jdenish1/MY_Kyria_Handwired_Split_Keyboard_Build/Info/Kyria_Handwired Key Matrix.jpeg

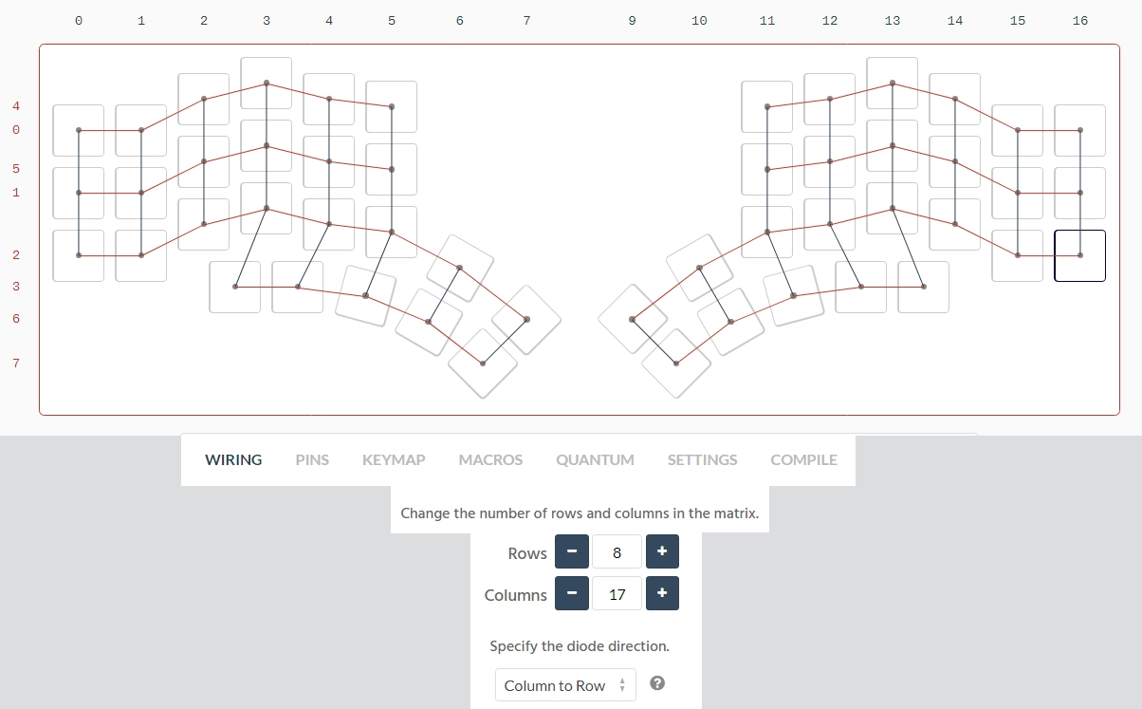
Info/Kyria_Handwired Key Matrix.jpeg
