jdenish1/MY_Kyria_Handwired_Split_Keyboard_Build/Pics/4 - Left Side 1.jpg

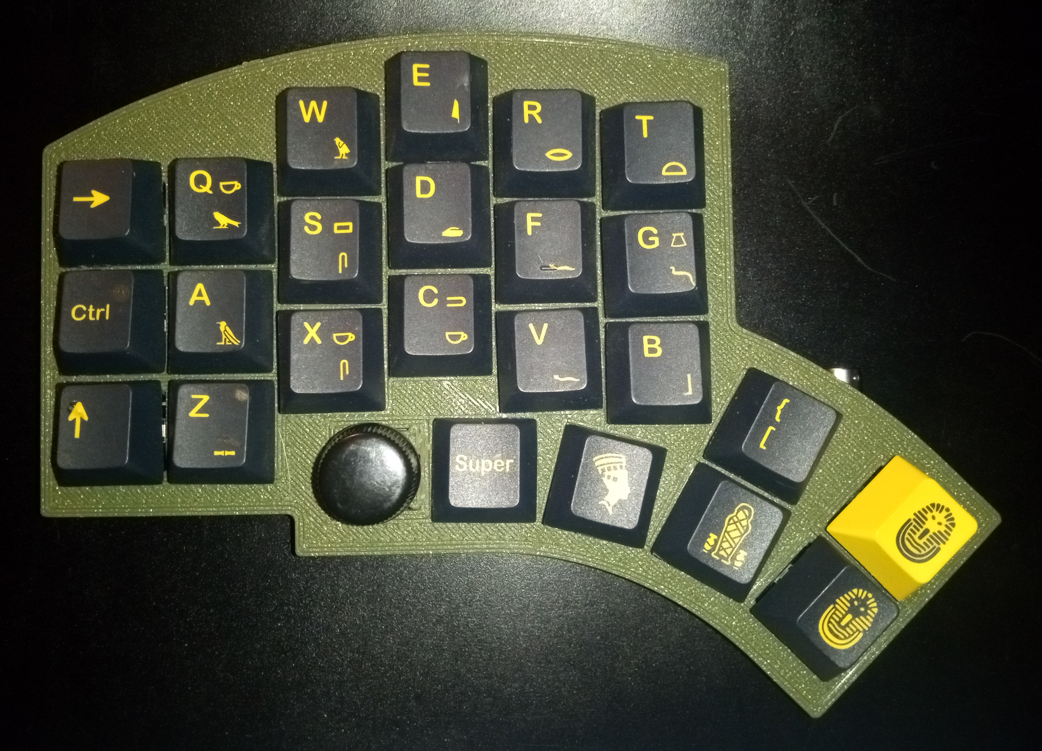
Pics/4 - Left Side 1.jpg
