jdenish1/MY_Kyria_Handwired_Split_Keyboard_Build/Pics/5 - Right Side 1.jpg

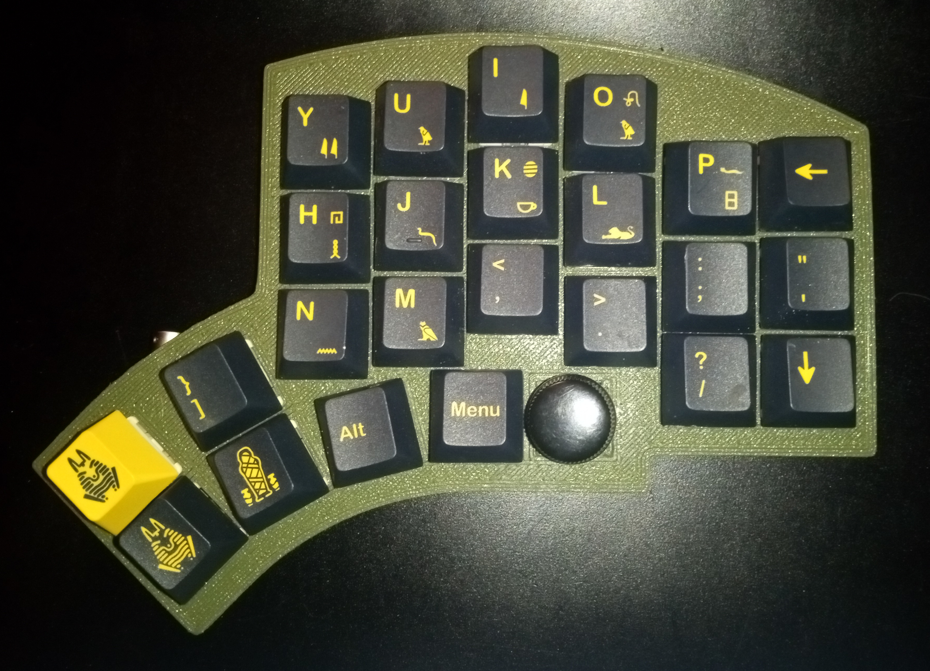
Pics/5 - Right Side 1.jpg
