jdenish1/MY_Kyria_Handwired_Split_Keyboard_Build/Pics/6 - Left Side 2.jpg

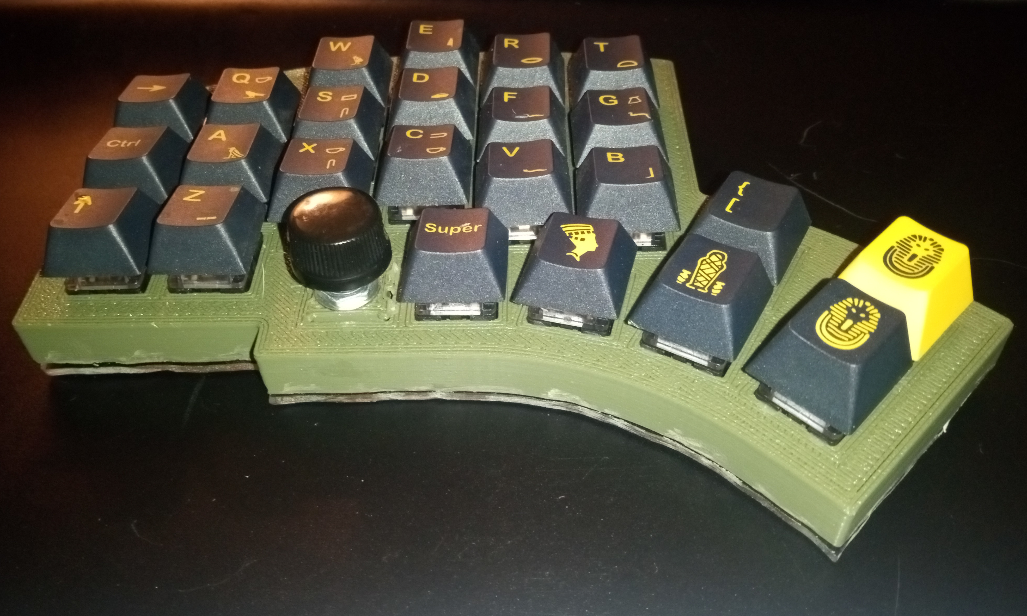
Pics/6 - Left Side 2.jpg
