jdenish1/MY_Kyria_Handwired_Split_Keyboard_Build/Pics/7 - Right Side 2.jpg

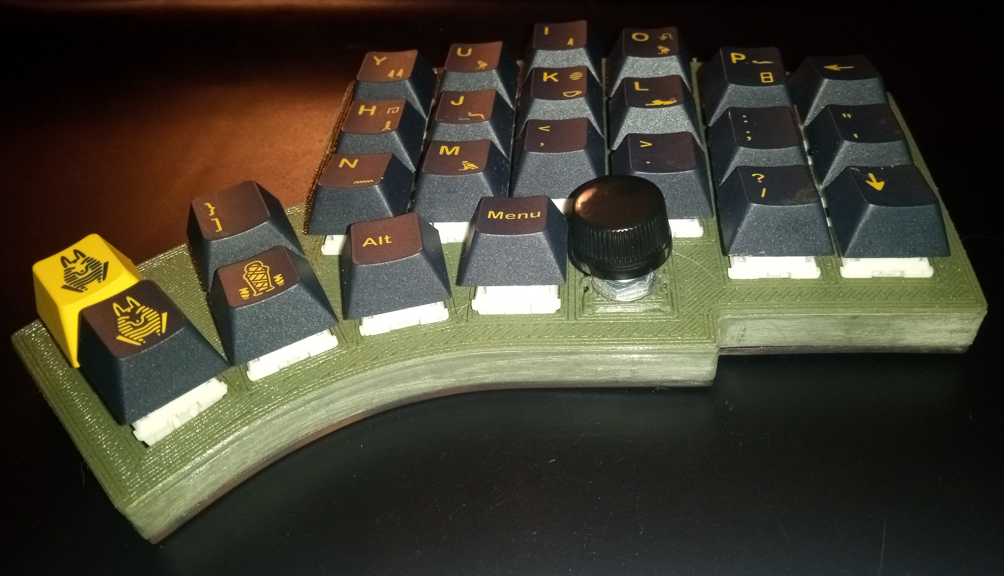
Pics/7 - Right Side 2.jpg
