jdenish1/MY_Kyria_Handwired_Split_Keyboard_Build/Pics/9 - Right Side 3.jpg

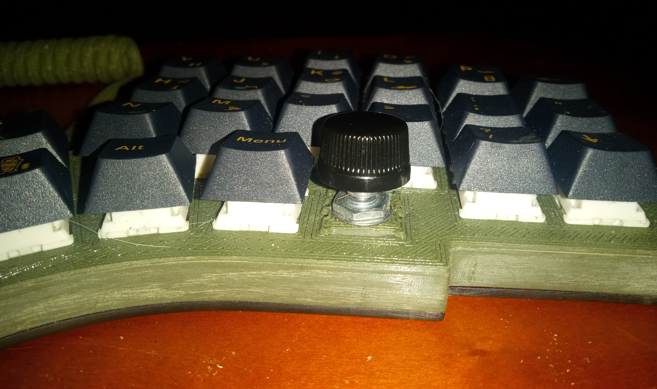
Pics/9 - Right Side 3.jpg
