jdenish1/MY_Kyria_Handwired_Split_Keyboard_Build/Pics/11 - XS6 Cable Closeup 2.jpg

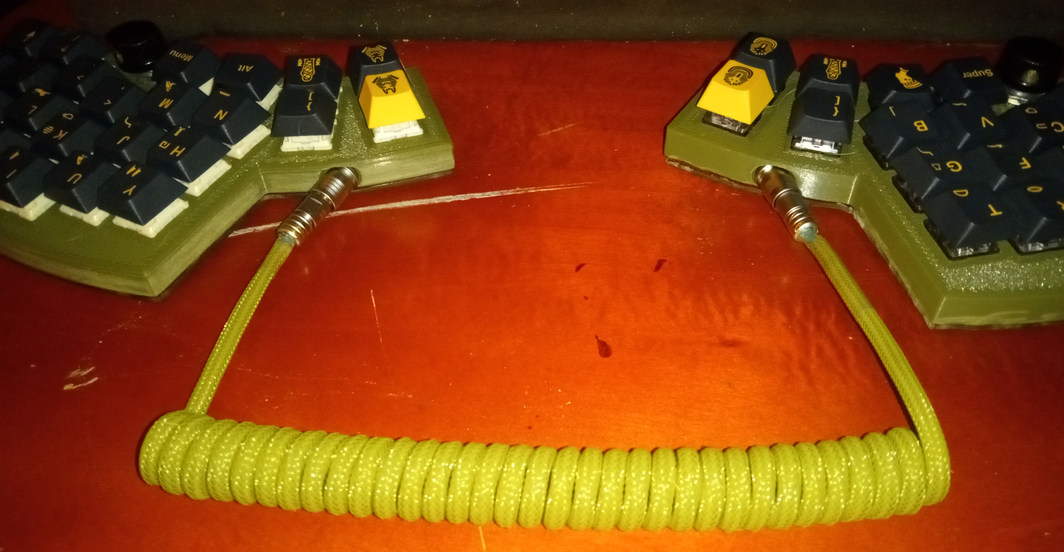
Pics/11 - XS6 Cable Closeup 2.jpg
