jdenish1/MY_Kyria_Handwired_Split_Keyboard_Build/Pics/15 - Left Side Acrylic Back Cover for Kyria_Handwired.jpg

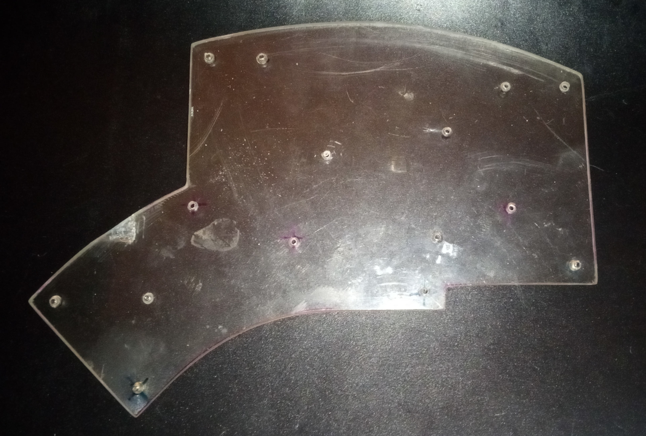
Pics/15 - Left Side Acrylic Back Cover for Kyria_Handwired.jpg
