jdenish1/MY_Kyria_Handwired_Split_Keyboard_Build/Pics/16 - Right Side Acrylic Back Cover for Kyria_Handwired.jpg

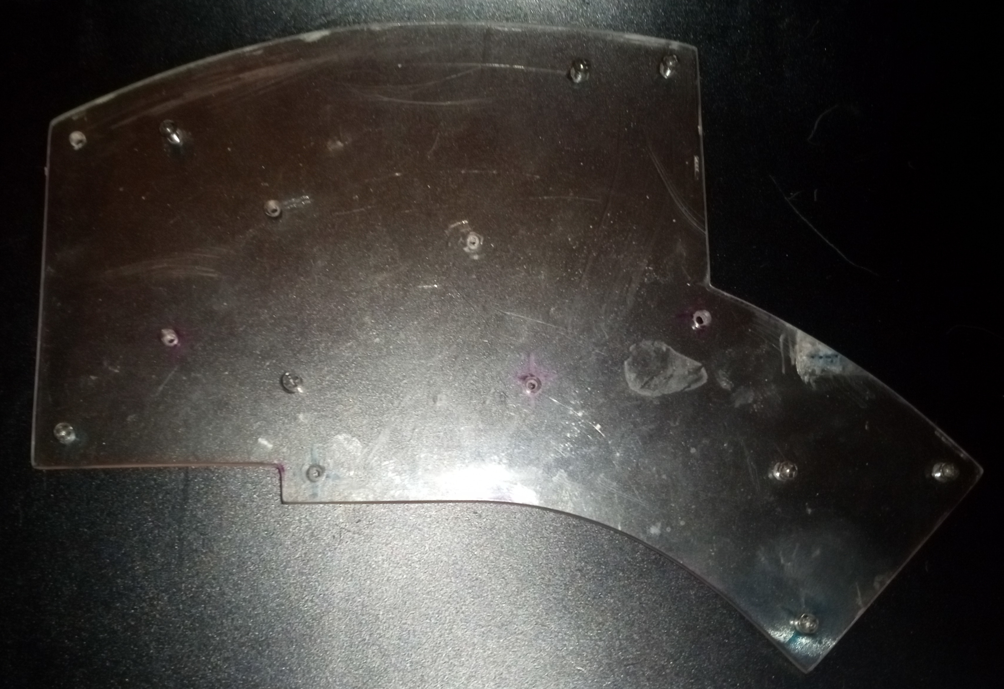
Pics/16 - Right Side Acrylic Back Cover for Kyria_Handwired.jpg
