jdenish1/MY_Kyria_Handwired_Split_Keyboard_Build/Pics/Whole Keyboard Cropped-compressed.png

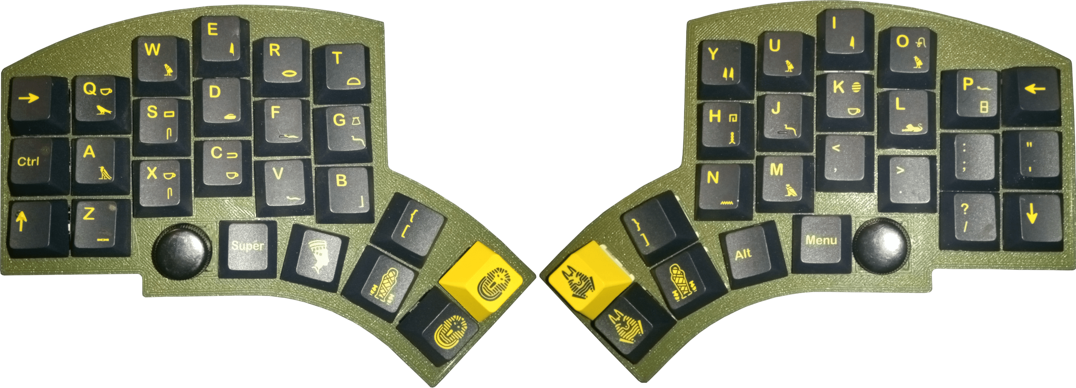
Pics/Whole Keyboard Cropped-compressed.png
