jdenish1/MY_Kyria_Handwired_Split_Keyboard_Build/Info/KYRIA_HANDWIRED_WIRING_DIAGRAM - COLUMNS ONLY.png

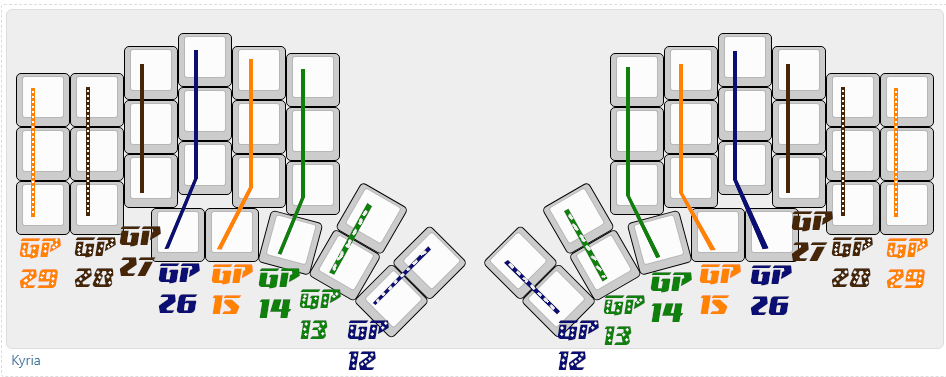
Info/KYRIA_HANDWIRED_WIRING_DIAGRAM - COLUMNS ONLY.png
