jdenish1/MY_Kyria_Handwired_Split_Keyboard_Build/Pics/3 - Completed Kyria Build 3.jpg

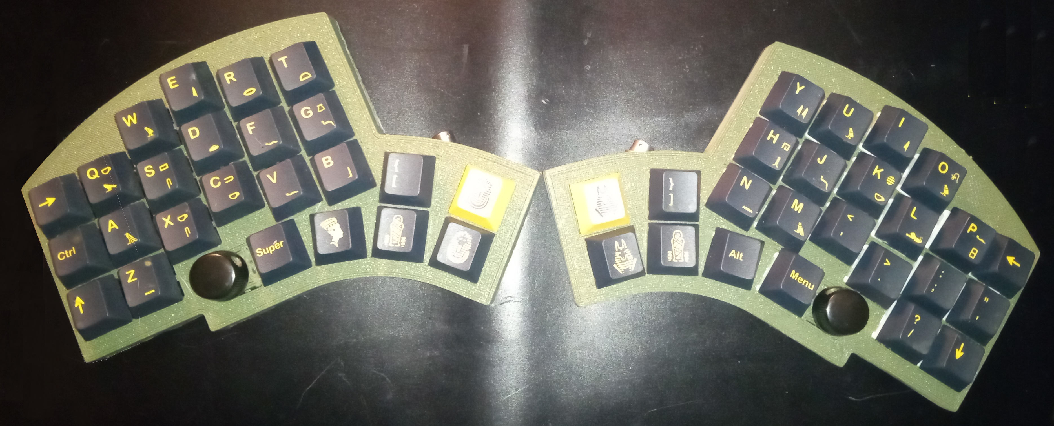
Pics/3 - Completed Kyria Build 3.jpg
