jdenish1/MY_Kyria_Handwired_Split_Keyboard_Build/Pics/13 - Underneath Left Side Wiring.jpg

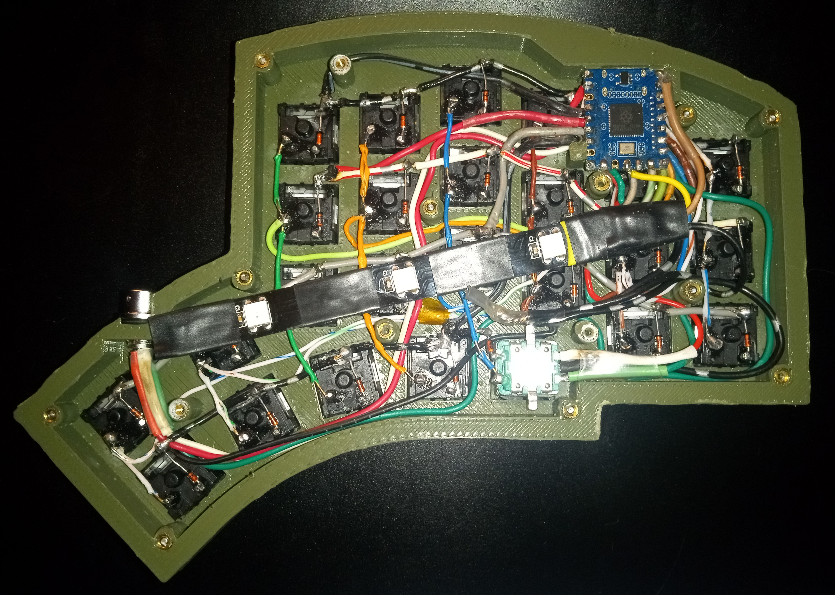
Pics/13 - Underneath Left Side Wiring.jpg
