jdenish1/MY_Kyria_Handwired_Split_Keyboard_Build/Pics/14 - Underneath Right Side Wiring.jpg

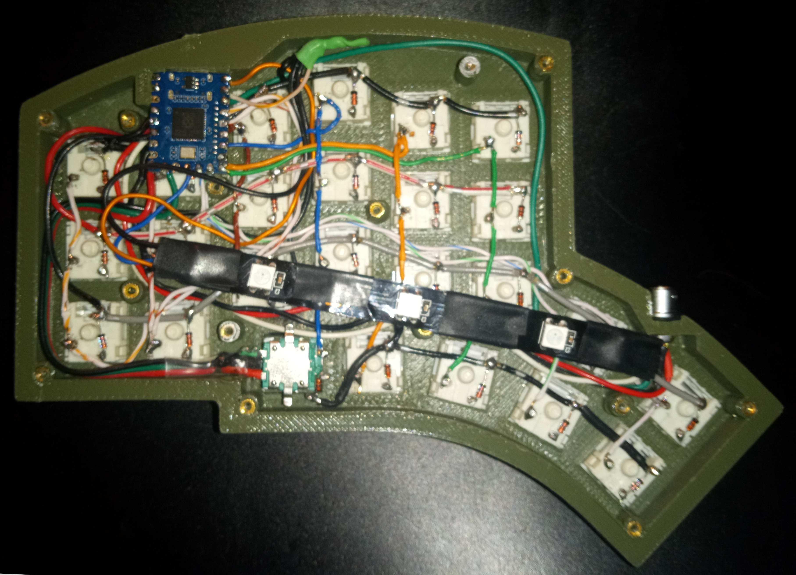
Pics/14 - Underneath Right Side Wiring.jpg
