jdenish1/MY_Kyria_Handwired_Split_Keyboard_Build/Firmware/3.VIAL FW/kyria_handwired/keymaps/vial/config.h

/* SPDX-License-Identifier: GPL-2.0-or-later */

#pragma once

#define VIAL_KEYBOARD_UID {0x9C, 0x9C, 0xB7, 0xD6, 0xD2, 0xC2, 0xBF, 0x89}
#define VIAL_UNLOCK_COMBO_ROWS { 0, 0 }
#define VIAL_UNLOCK_COMBO_COLS { 0, 1 }
