jdenish1/MY_Kyria_Handwired_Split_Keyboard_Build/Firmware/1.QMK FW/Firmware/Kyria_Handwired/Keymaps/jdenish1/qmk_rc.c

#include <stdlib.h>
#include "qmk_rc.h"

#ifndef QMK_RC_DISABLE_DEFAULT_COMMANDS
#  include <string.h>
#  include "quantum.h"
#  ifdef OLED_DRIVER_ENABLE
#    include "oled_driver.h"
#  endif
#  ifdef RGBLIGHT_ENABLE
#    include "rgblight.h"
#  endif
#  ifdef RGB_MATRIX_ENABLE
#    include "rgb_matrix.h"
#  endif
#endif

__attribute__((weak)) void qmk_rc_process_command_user(qmk_rc_command_t* command) { }


enum qmk_rc_commands_quantum {
  RESERVED = 0,
#ifndef QMK_RC_DISABLE_DEFAULT_COMMANDS

  RGBLIGHT_OFF,
  RGBLIGHT_ON,
  // RGBLIGHT_SETRGB_RANGE and RGB_MATRIX_SETRGB_RANGE accept 5 data bytes:
  // R - G - B - I0 - I1
  // * RGB - the color
  // * I0 - the LED index start
  // * I1 - the LED index end
  RGBLIGHT_SETRGB_RANGE,

  RGB_MATRIX_OFF,
  RGB_MATRIX_ON,
  RGB_MATRIX_SETRGB_RANGE,

  LAYER_ON,
  LAYER_OFF,
  LAYER_CLEAR,
  LAYER_MOVE,

  SEND_STRING,
#endif
};

#ifndef QMK_RC_DISABLE_DEFAULT_COMMANDS
void qmk_rc_process_command_quantum(qmk_rc_command_t* command) {
  switch (command->id) {

#ifdef RGBLIGHT_ENABLE
    case RGBLIGHT_OFF: rgblight_disable_noeeprom(); break;
    case RGBLIGHT_ON: rgblight_enable_noeeprom(); break;
    case RGBLIGHT_SETRGB_RANGE:
      rgblight_setrgb_range(
        command->data[0], // R
        command->data[1], // G
        command->data[2], // B
        command->data[3], // diode index start
        command->data[4]  // diode index end
      );
      break;
#endif

#ifdef RGB_MATRIX_ENABLE
    case RGB_MATRIX_OFF: rgb_matrix_disable_noeeprom(); break;
    case RGB_MATRIX_ON: rgb_matrix_enable_noeeprom(); break;
    case RGB_MATRIX_SETRGB_RANGE:
      for (int i = command->data[3]; i < command->data[4]; i++)
        rgb_matrix_set_color(i, command->data[0], command->data[1], command->data[2]);
      break;
#endif

    case LAYER_ON: layer_on(command->data[0]); break;
    case LAYER_OFF: layer_off(command->data[0]); break;
    case LAYER_CLEAR: layer_clear(); break;
    case LAYER_MOVE: layer_move(command->data[0]); break;

    case SEND_STRING: send_string((const char*) command->data); break;

    default:
      qmk_rc_process_command_user(command);
  }
}
#else
#  define qmk_rc_process_command_quantum qmk_rc_process_command_user
#endif

qmk_rc_parser_t parser = {
  .state = RECEIVING_COMMAND,
  .data_bytes_read = 0,
};

qmk_rc_command_t command = {
  .id = UINT8_MAX,
  .data_length = 0,
  .data = NULL,
};

void qmk_rc_receive(uint8_t *buffer, uint16_t max_buffer_length, uint8_t* data, uint8_t data_length) {
  for (int i = 0; i < data_length; i++) {
    if (parser.state == RECEIVING_COMMAND) {
      // Raw HID packets are padded to `RAW_EPSIZE`, 32 or 64 bytes. Since this
      // is an afterthought for this parser, we reserve the 0 command code as
      // a "skip" instruction in receiving command mode. In the sender we then
      // universally pad to 64 bytes with 0s.
      if (data[i] == 0) continue;

      command.id = data[i];
      parser.state = RECEIVING_DATA_LENGTH;

      parser.data_length_bytes_read = 0;
      parser.data_length.data_length = 0;
    }
    else if (parser.state == RECEIVING_DATA_LENGTH) {
      parser.data_length.raw[parser.data_length_bytes_read++] = data[i];

      if (parser.data_length_bytes_read == sizeof(qmk_rc_data_length_t)) {
        command.data_length = parser.data_length.data_length;

        command.data = NULL;

        if (command.data_length == 0) {
          qmk_rc_process_command_quantum(&command);
          parser.state = RECEIVING_COMMAND;
        }
        else {
          parser.state = RECEIVING_DATA;
          parser.data_bytes_read = 0;
        }
      }
    }
    else if (parser.state == RECEIVING_DATA) {
      buffer[parser.data_bytes_read++] = data[i];
      if (parser.data_bytes_read == command.data_length) {
        command.data = buffer;
        qmk_rc_process_command_quantum(&command);
        parser.state = RECEIVING_COMMAND;
      }
    }
  }
}
